anthal/Display-VQC10/Images/20260331_211946.jpg

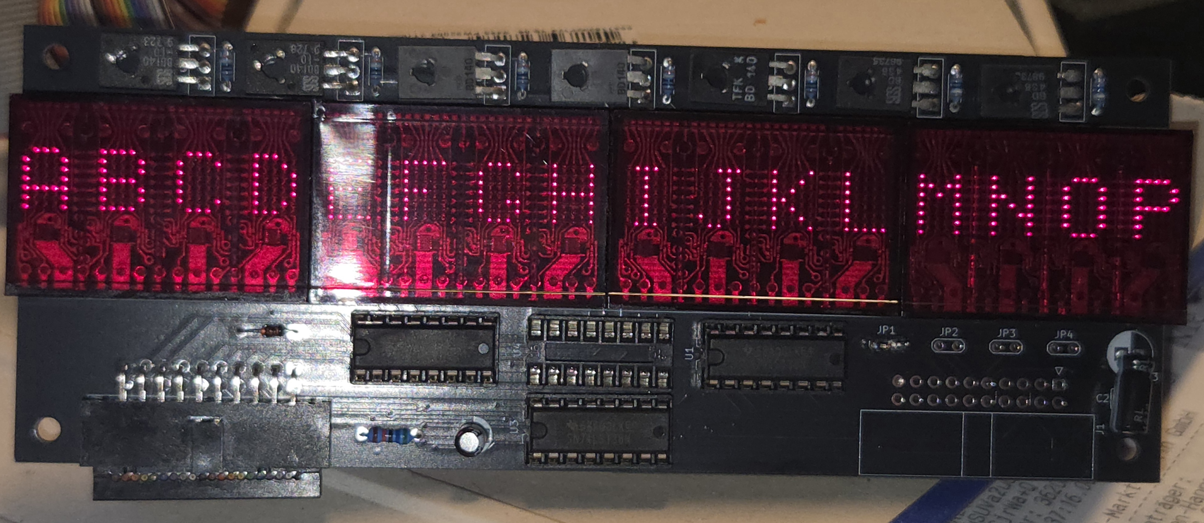
Images/20260331_211946.jpg
