anthal/Display-VQC10/Software/Micropython/bitmap5x7.py

# © Kay Sievers <kay@versioduo.com>, 2022
# SPDX-License-Identifier: Apache-2.0

font5x7 = [
    [0x00, 0x00, 0x00, 0x00, 0x00], # " "
    [0x00, 0x00, 0x5F, 0x00, 0x00], # !
    [0x00, 0x07, 0x00, 0x07, 0x00], # "
    [0x14, 0x7F, 0x14, 0x7F, 0x14], # #
    [0x24, 0x2A, 0x7F, 0x2A, 0x12], # $
    [0x23, 0x13, 0x08, 0x64, 0x62], # %
    [0x36, 0x49, 0x55, 0x22, 0x50], # &
    [0x00, 0x05, 0x03, 0x00, 0x00], # '
    [0x00, 0x1C, 0x22, 0x41, 0x00], # (
    [0x00, 0x41, 0x22, 0x1C, 0x00], # )
    [0x08, 0x2A, 0x1C, 0x2A, 0x08], # *
    [0x08, 0x08, 0x3E, 0x08, 0x08], # +
    [0x00, 0x50, 0x30, 0x00, 0x00], # ,
    [0x08, 0x08, 0x08, 0x08, 0x08], # -
    [0x00, 0x60, 0x60, 0x00, 0x00], # .
    [0x20, 0x10, 0x08, 0x04, 0x02], # /
    [0x3E, 0x51, 0x49, 0x45, 0x3E], # 0
    [0x00, 0x42, 0x7F, 0x40, 0x00], # 1
    [0x42, 0x61, 0x51, 0x49, 0x46], # 2
    [0x21, 0x41, 0x45, 0x4B, 0x31], # 3
    [0x18, 0x14, 0x12, 0x7F, 0x10], # 4
    [0x27, 0x45, 0x45, 0x45, 0x39], # 5
    [0x3C, 0x4A, 0x49, 0x49, 0x30], # 6
    [0x01, 0x71, 0x09, 0x05, 0x03], # 7
    [0x36, 0x49, 0x49, 0x49, 0x36], # 8
    [0x06, 0x49, 0x49, 0x29, 0x1E], # 9
    [0x00, 0x36, 0x36, 0x00, 0x00], # :
    [0x00, 0x56, 0x36, 0x00, 0x00], # ;
    [0x00, 0x08, 0x14, 0x22, 0x41], # <
    [0x14, 0x14, 0x14, 0x14, 0x14], # =
    [0x41, 0x22, 0x14, 0x08, 0x00], # >
    [0x02, 0x01, 0x51, 0x09, 0x06], # ?
    [0x32, 0x49, 0x79, 0x41, 0x3E], # @
    [0x7E, 0x09, 0x09, 0x09, 0x7E], # A
    [0x7F, 0x49, 0x49, 0x49, 0x36], # B
    [0x3E, 0x41, 0x41, 0x41, 0x22], # C
    [0x7F, 0x41, 0x41, 0x22, 0x1C], # D
    [0x7F, 0x49, 0x49, 0x49, 0x41], # E
    [0x7F, 0x09, 0x09, 0x01, 0x01], # F
    [0x3E, 0x41, 0x41, 0x51, 0x32], # G
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
]


#const uint8_t *Font5x7::getBitmap(uint8_t character) [
def getBitmap(character):
    #if (character < 0x20 or character > 0x7e):
    if (character < 0x20):
        return font5x7[0]
    else:
        return font5x7[character - 0x20]
